balassy/useless-box/status-led.cpp

#include "status-led.h"

void StatusLed::setPin(uint8_t pin) {
  pinMode(pin, OUTPUT);
  _pin = pin;
}

void StatusLed::turnOn() {
   digitalWrite(_pin, LOW);
}

void StatusLed::turnOff() {
   digitalWrite(_pin, HIGH);
}
